DCC-EX/T3-EX-Tethered/src/Functions.h

#ifndef FUNCTIONS_H
#define FUNCTIONS_H

#include <Arduino.h>

// Division and ceil without needing double
// https://stackoverflow.com/questions/2745074/fast-ceiling-of-an-integer-division-in-c-c#comment32189462_2745074
// https://stackoverflow.com/a/14878734
/**
 * @brief Divide and Ceil
 * 
 * @param i number
 * @param div divide by
 * @return uint8_t 
 */
inline uint8_t divideAndCeil(uint8_t i, uint8_t div) {
  return i / div + (i % div != 0);
}

#endif
